schlae/XebecAboveBoard/XebecMem.kicad_sch

## KiCad design XebecMem.kicad_sch (2024-04-21)

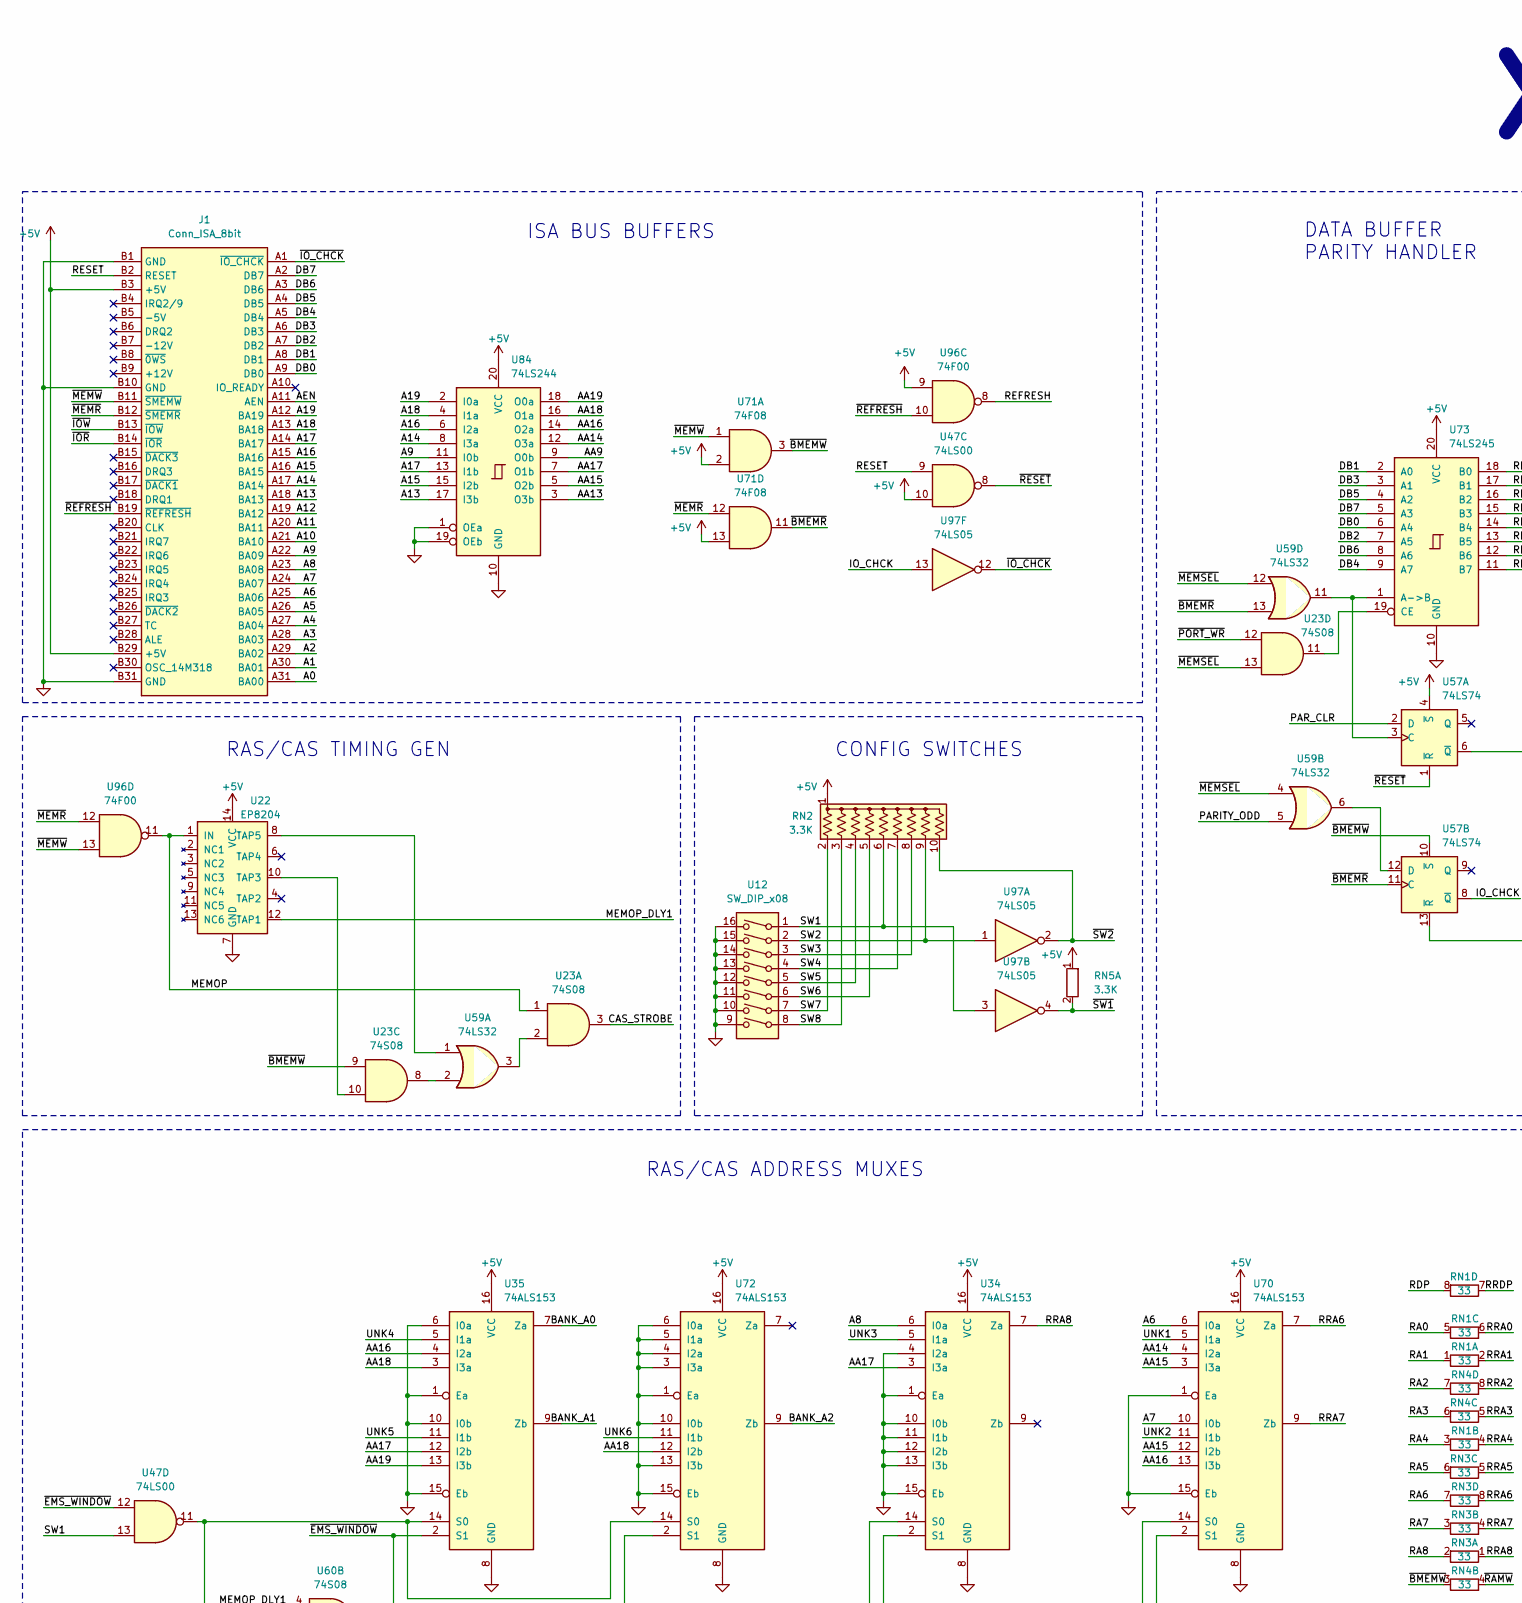
[picture p2: schematic XebecMem.kicad_sch, part in row 1, column 1]

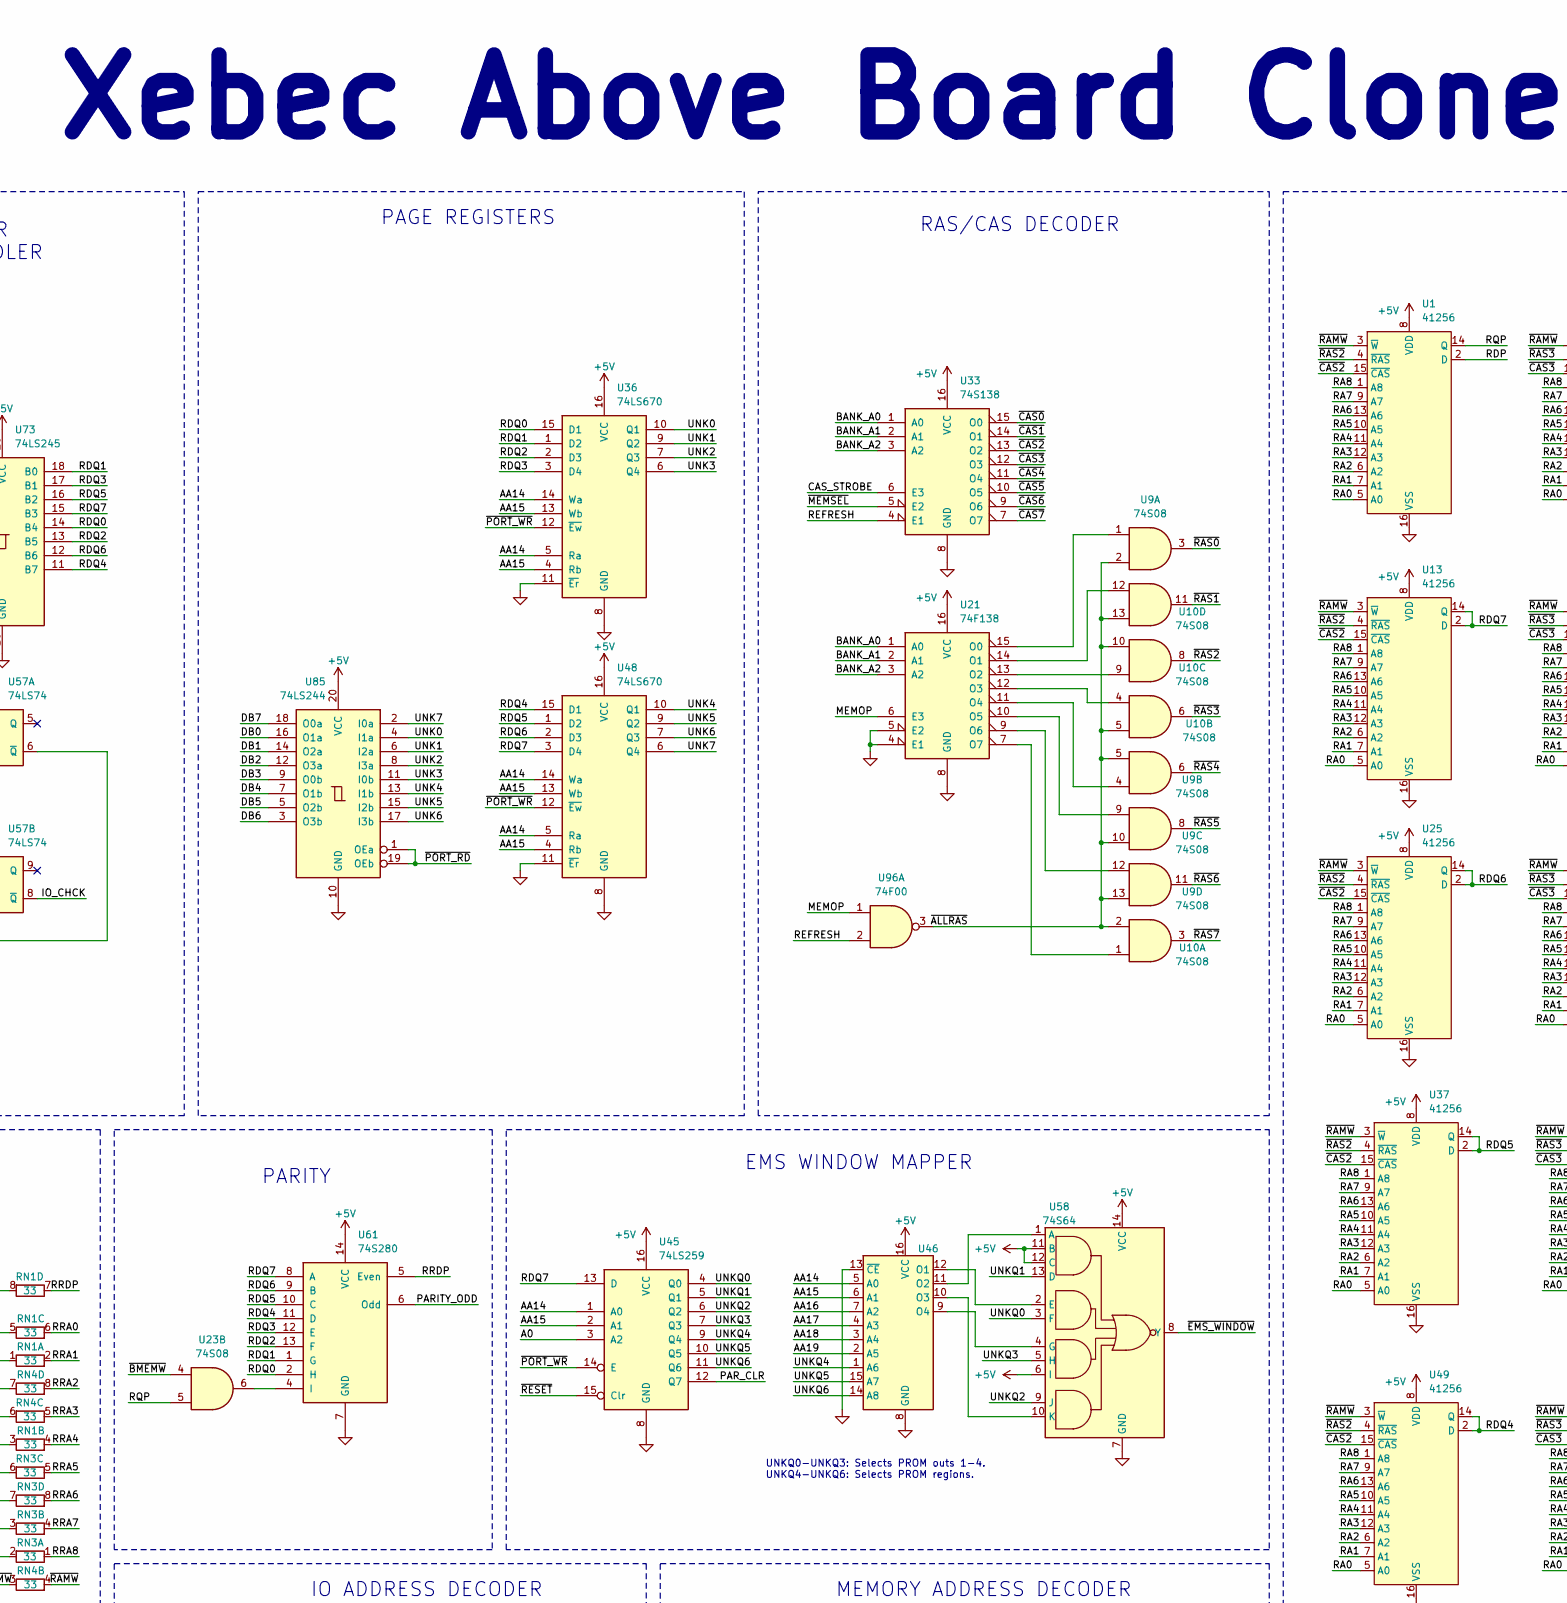
[picture p3: schematic XebecMem.kicad_sch, part in row 1, column 2]

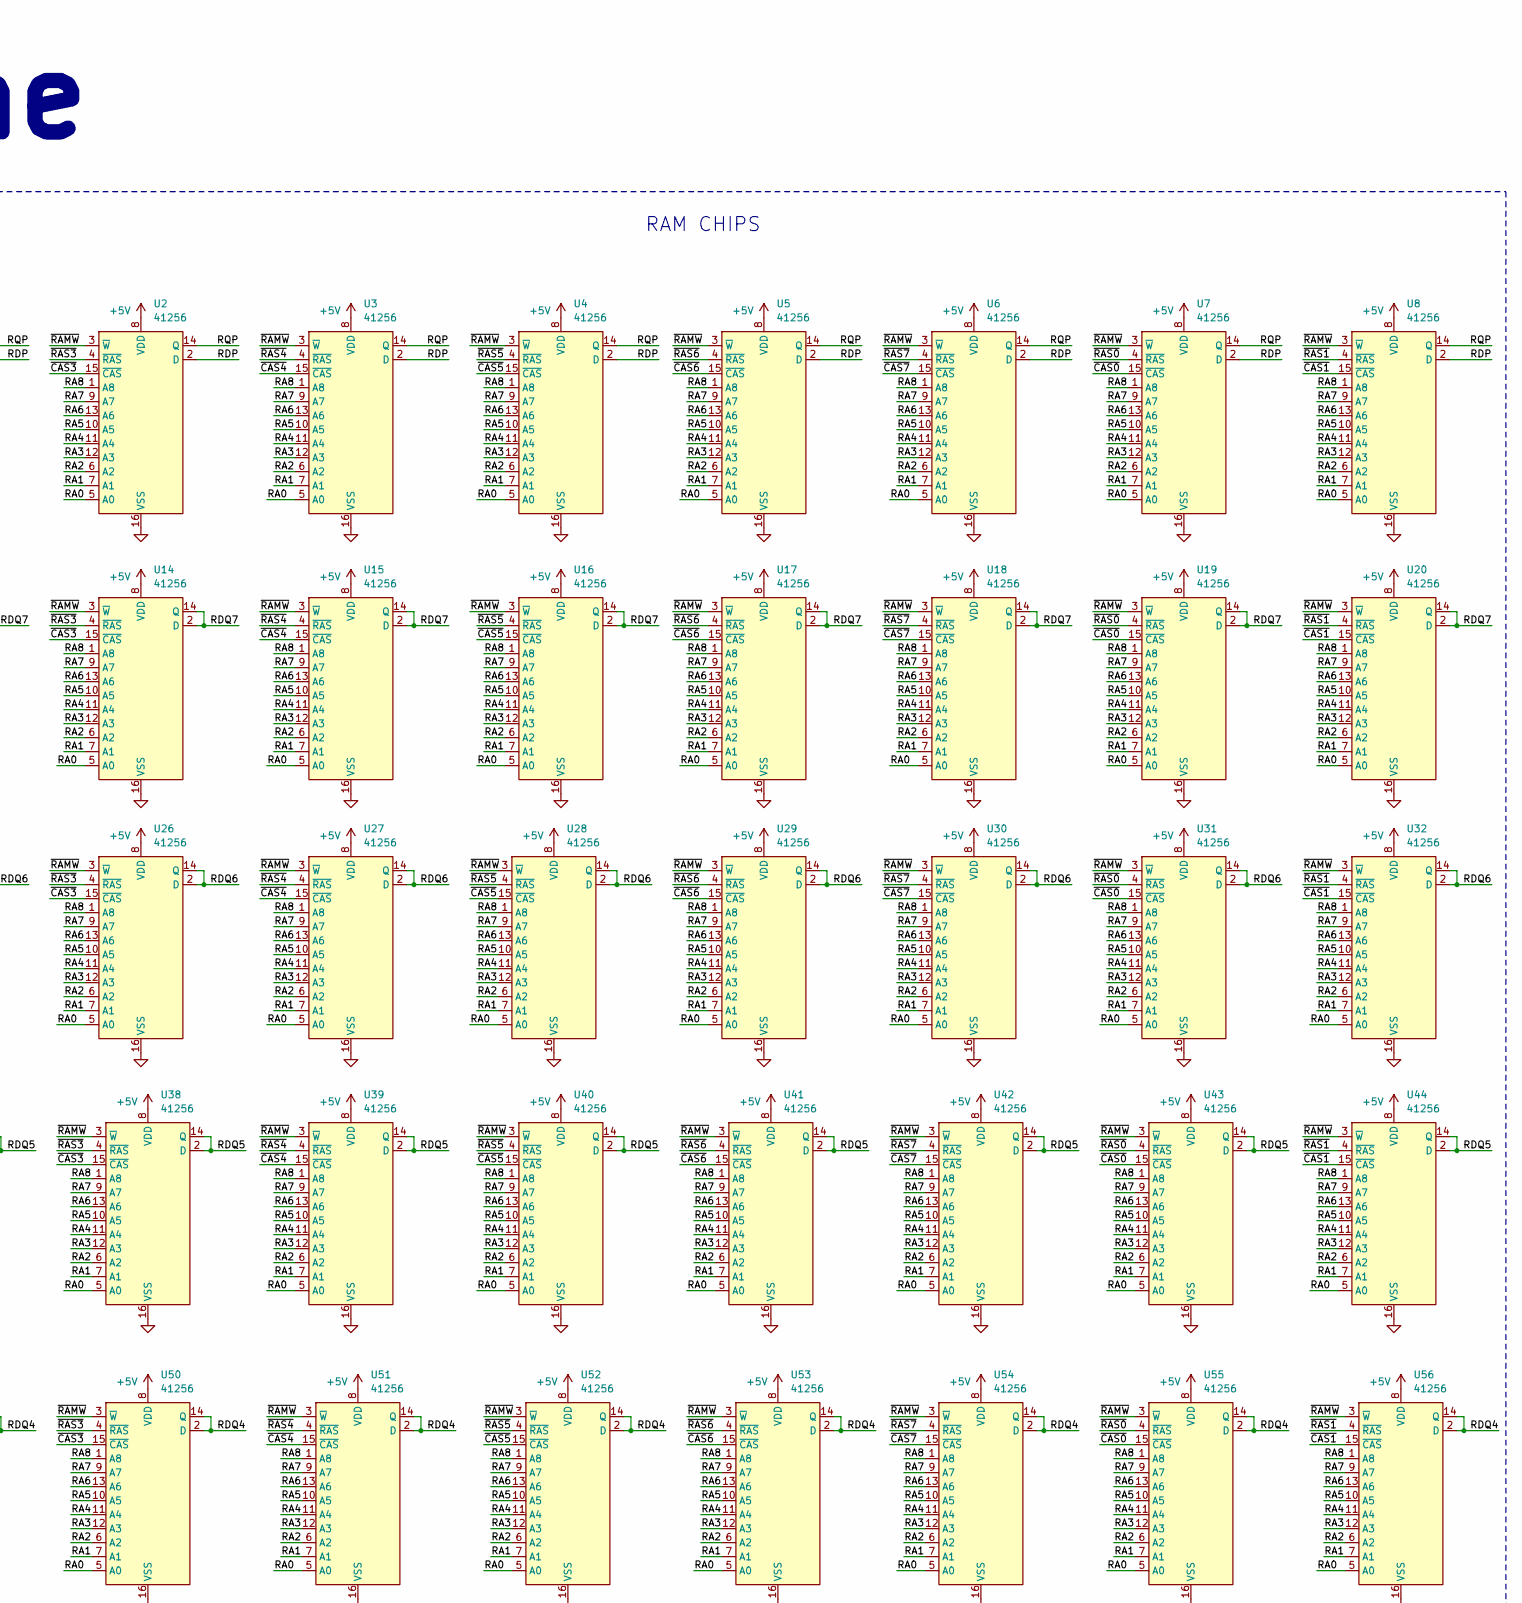
[picture p4: schematic XebecMem.kicad_sch, part in row 1, column 3]

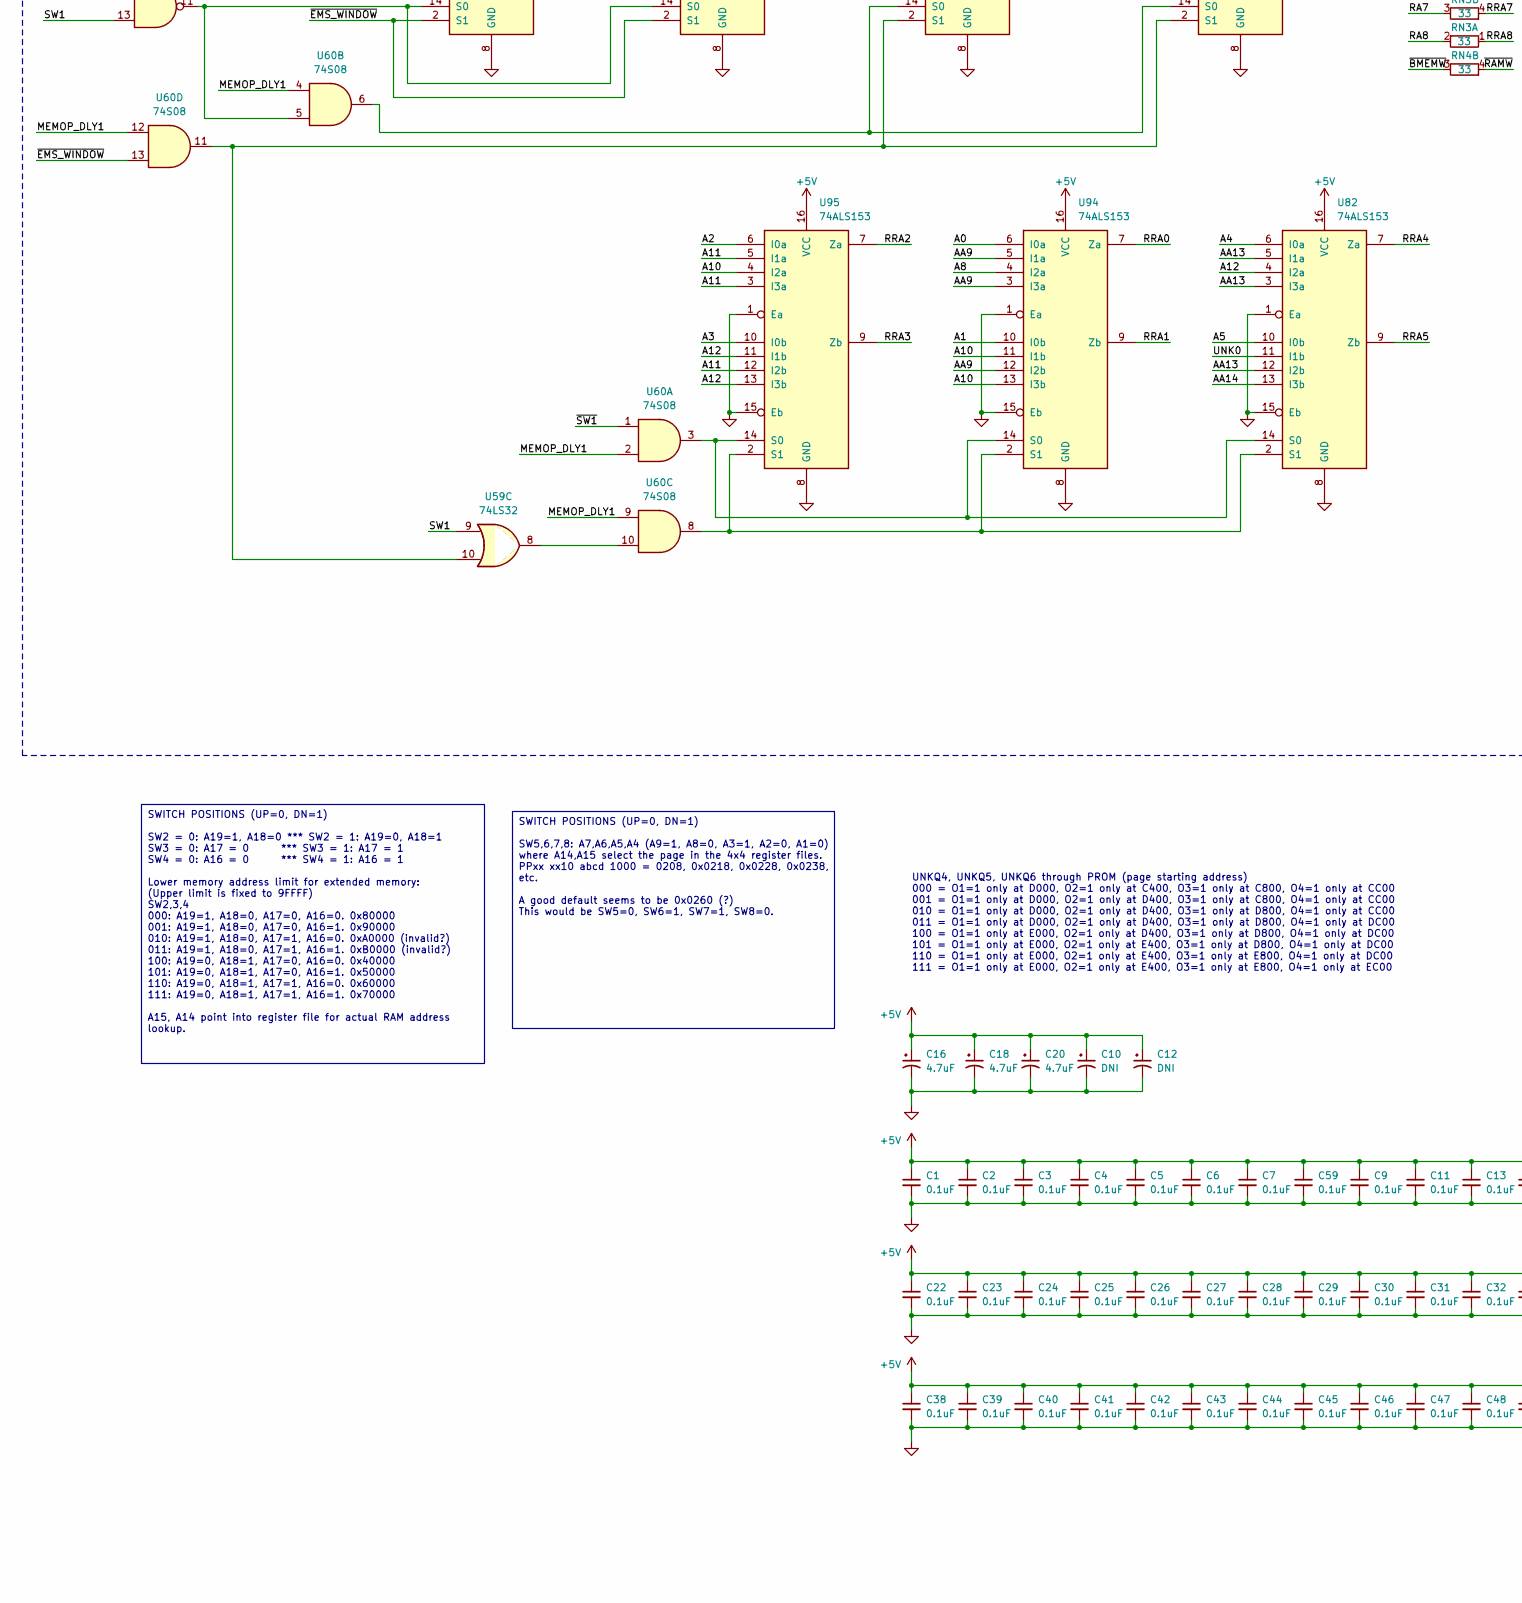
[picture p5: schematic XebecMem.kicad_sch, part in row 2, column 1]

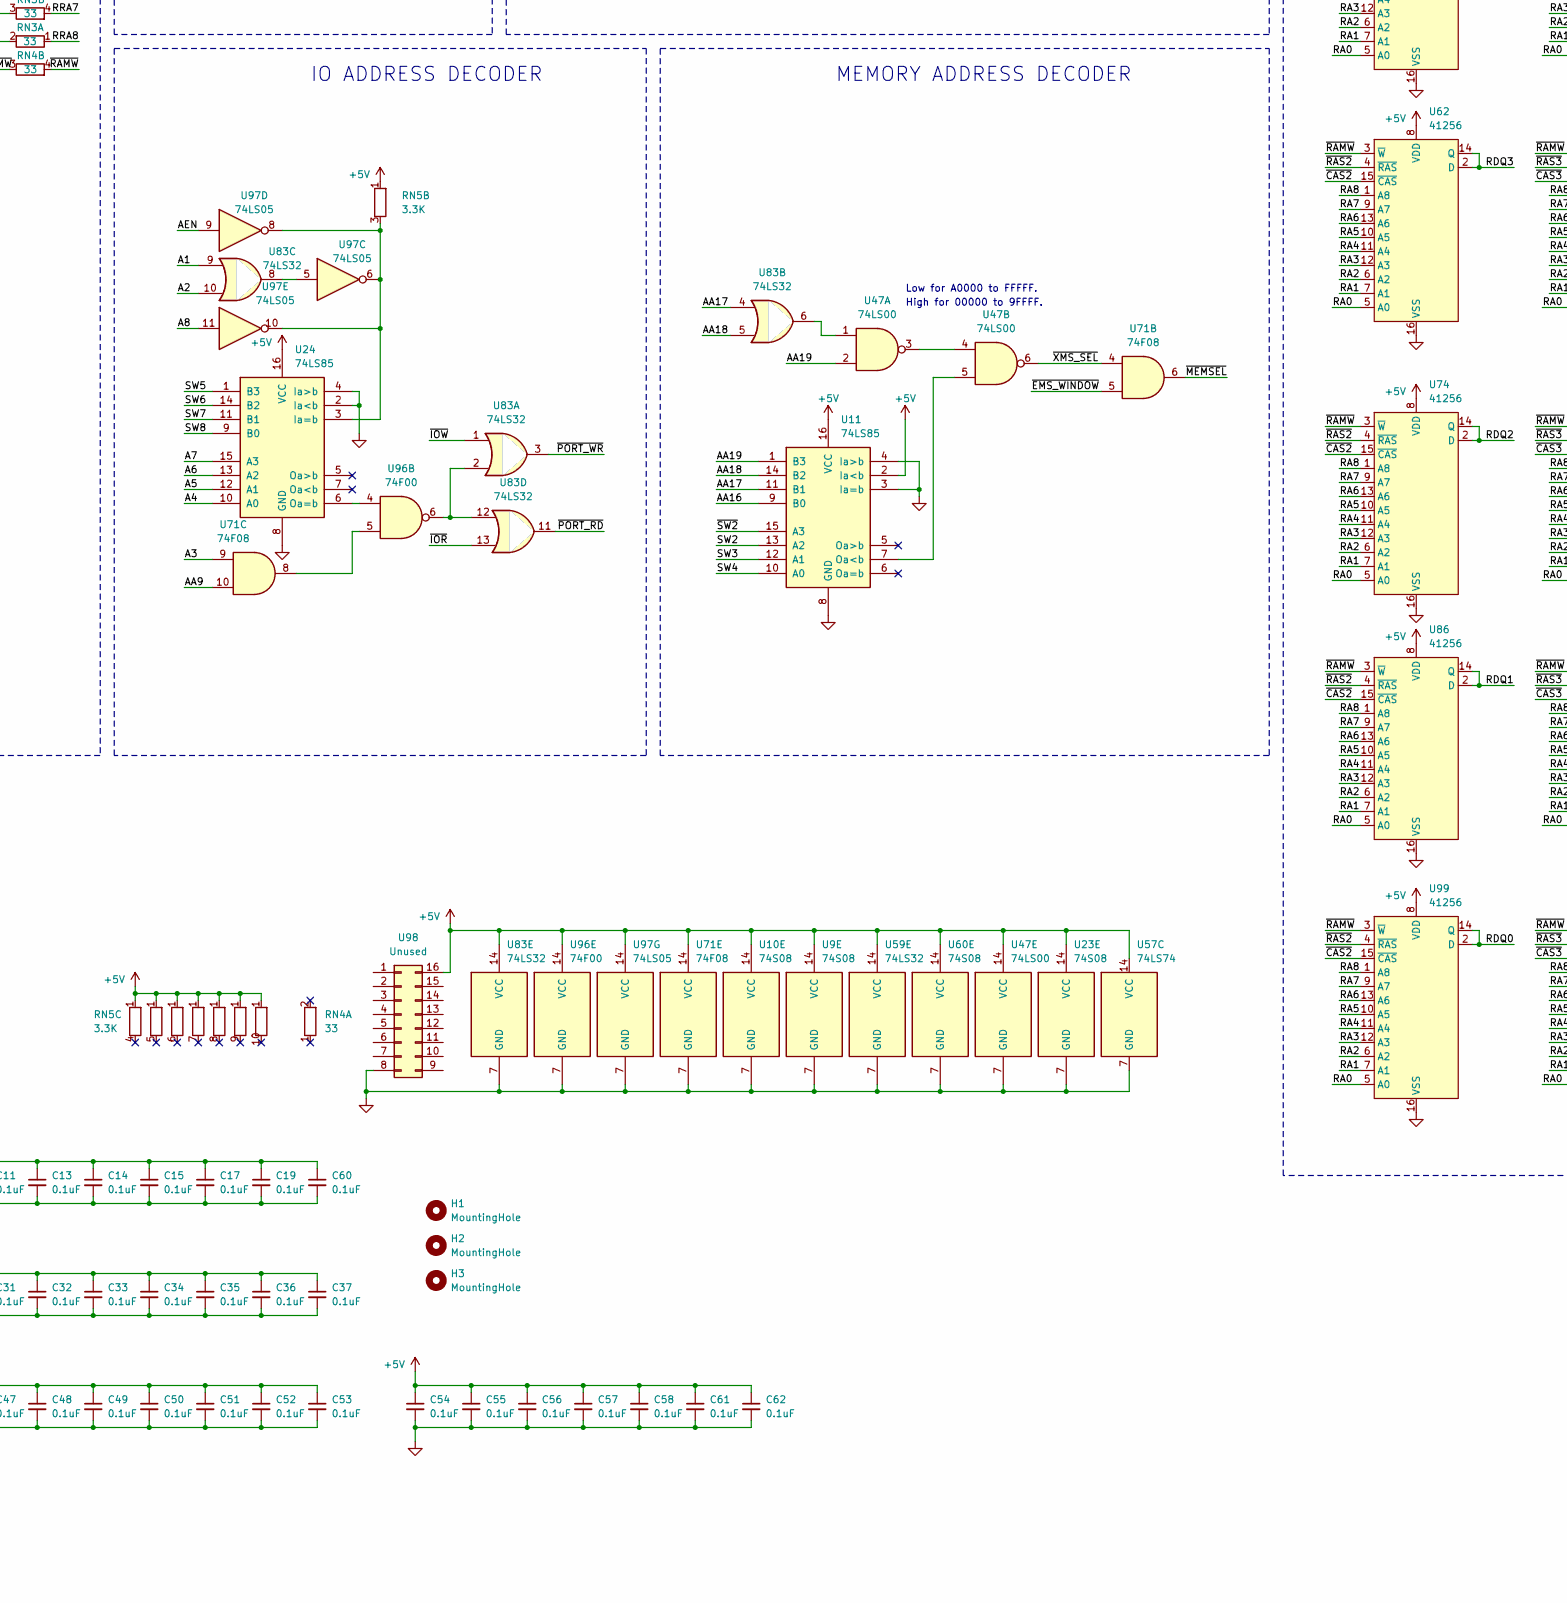
[picture p6: schematic XebecMem.kicad_sch, part in row 2, column 2]

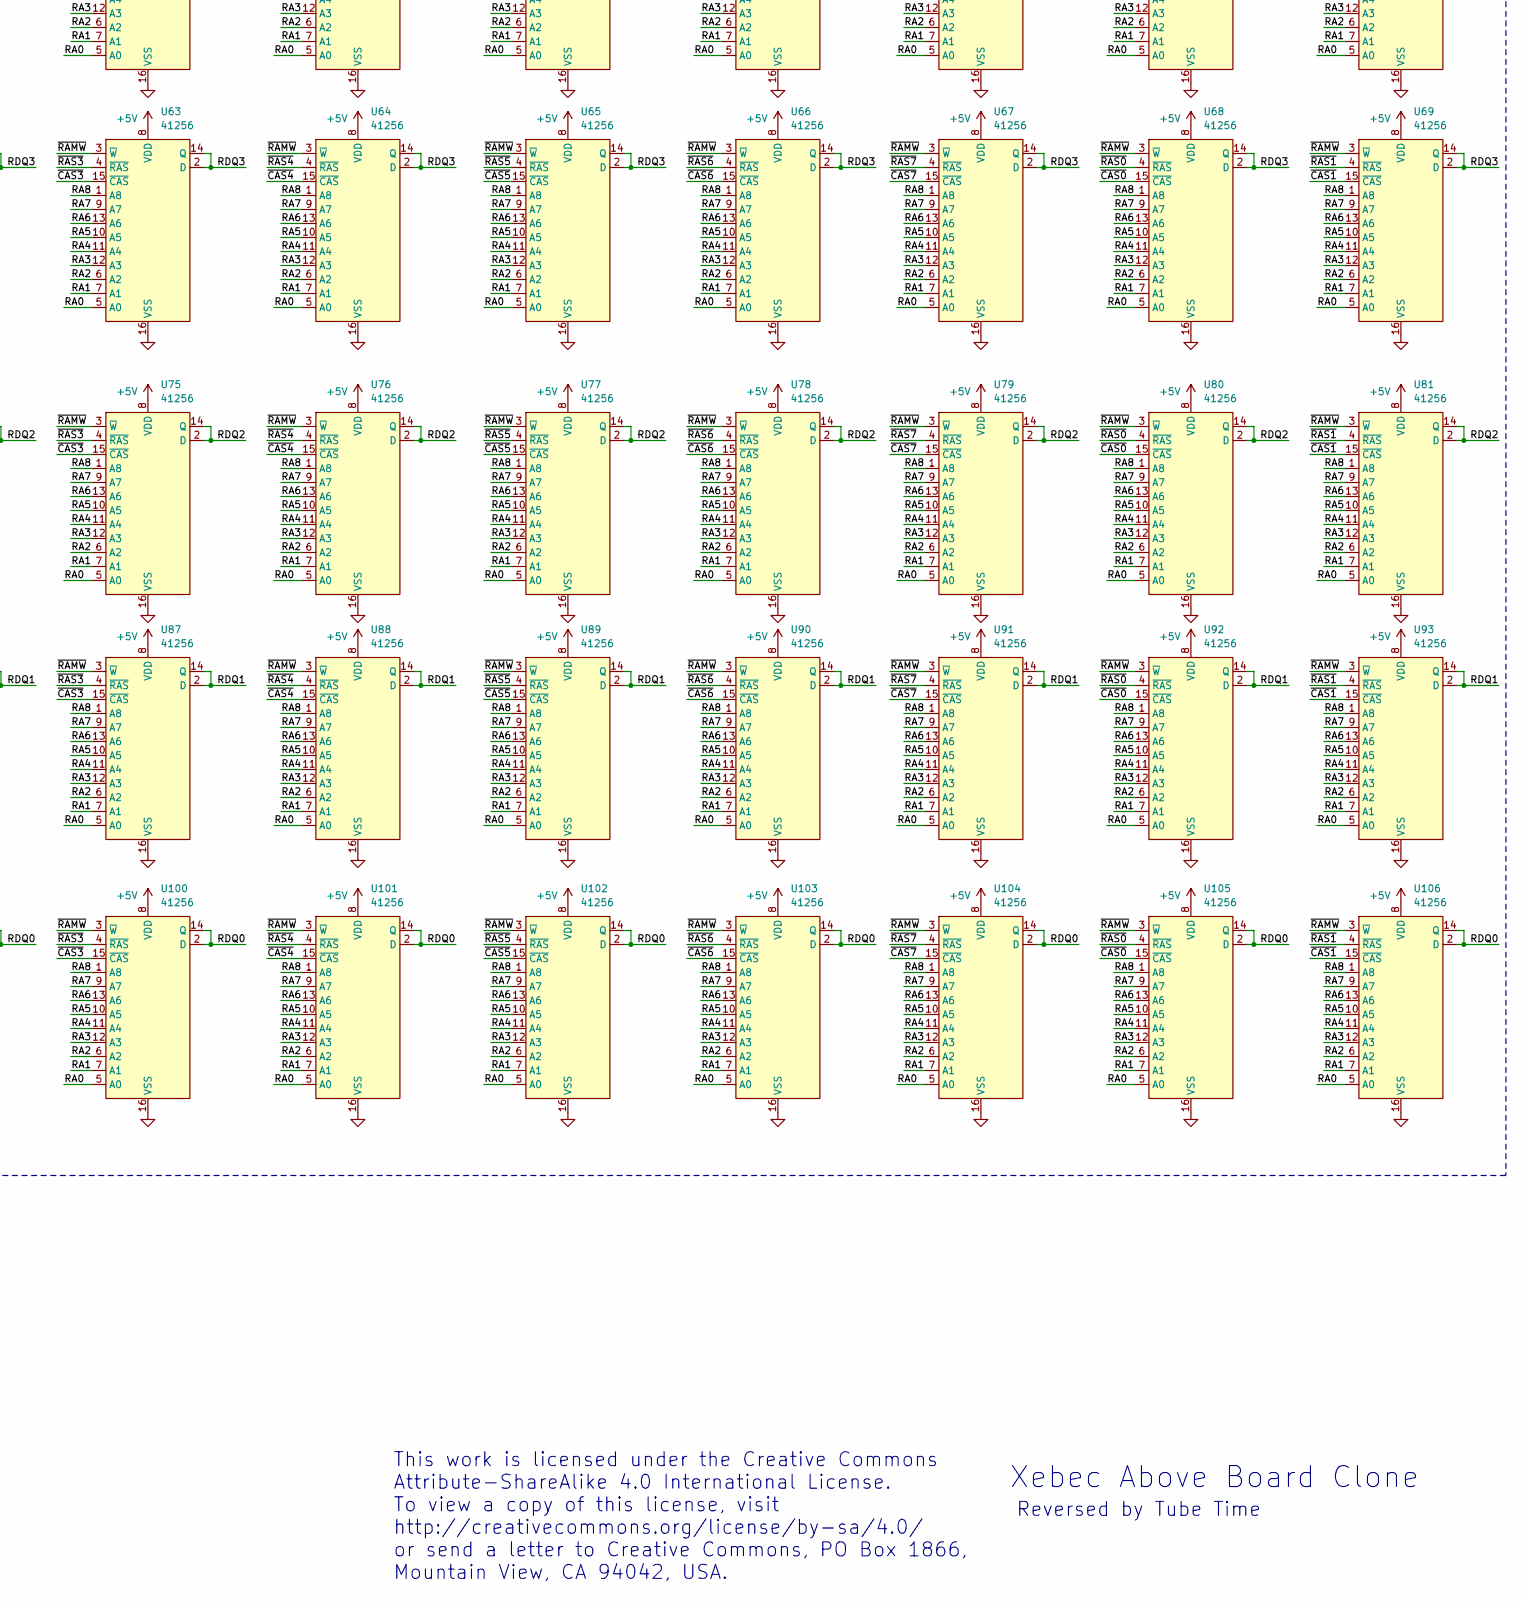
[picture p7: schematic XebecMem.kicad_sch, part in row 2, column 3]

Parts:
C1, C2, C3, C4, C5, C6, C7, C9, C11, C13, C14, C15, C17, C19, C22, C23, C24, C25, C26, C27, C28, C29, C30, C31, C32, C33, C34, C35, C36, C37, C38, C39, C40, C41, C42, C43, C44, C45, C46, C47, C48, C49, C50, C51, C52, C53, C54, C55, C56, C57, C58, C59, C60, C61, C62: 0.1uF; C_Axial_L3.8mm_D2.6mm_P7.50mm_Horizontal
C10, C12: DNI; C_Axial_L3.8mm_D2.6mm_P12.50mm_Horizontal
C16, C18, C20: 4.7uF; C_Axial_L3.8mm_D2.6mm_P12.50mm_Horizontal
H1, H2, H3: MountingHole; MountingHole_3mm
J1: Conn_ISA_8bit; BUS_PC_8BIT
RN1, RN3, RN4: 33; R_Array_SIP8
RN2, RN5: 3.3K; R_Array_SIP10
U1, U2, U3, U4, U5, U6, U7, U8, U13, U14, U15, U16, U17, U18, U19, U20, U25, U26, U27, U28, U29, U30, U31, U32, U37, U38, U39, U40, U41, U42, U43, U44, U49, U50, U51, U52, U53, U54, U55, U56, U62, U63, U64, U65, U66, U67, U68, U69, U74, U75, U76, U77, U78, U79, U80, U81, U86, U87, U88, U89, U90, U91, U92, U93, U99, U100, U101, U102, U103, U104, U105, U106: 41256; DIP254P762X635-16
U9, U10, U23, U60: 74S08; DIP254P762X635-14
U11, U24: 74LS85; DIP254P762X635-16
U12: SW_DIP_x08; DIP254P762X635-16
U21: 74F138; DIP254P762X635-16
U22: EP8204; DIP254P762X635-14
U33: 74S138; DIP254P762X635-16
U34, U35, U70, U72, U82, U94, U95: 74ALS153; DIP254P762X635-16
U36, U48: 74LS670; DIP254P762X635-16
U45: 74LS259; DIP254P762X635-16
U46: DIP254P762X635-16
U47: 74LS00; DIP254P762X635-14
U57: 74LS74; DIP254P762X635-14
U58: 74S64; DIP254P762X635-14
U59, U83: 74LS32; DIP254P762X635-14
U61: 74S280; DIP254P762X635-14
U71: 74F08; DIP254P762X635-14
U73: 74LS245; DIP254P762X635-20
U84, U85: 74LS244; DIP254P762X635-20
U96: 74F00; DIP254P762X635-14
U97: 74LS05; DIP254P762X635-14
U98: Unused; DIP254P762X635-16

Connections:
+5V: C1.1, C2.1, C3.1, C4.1, C5.1, C6.1, C7.1, C9.1, C10.1, C11.1, C12.1, C13.1, C14.1, C15.1, C16.1, C17.1, C18.1, C19.1, C20.1, C22.1, C23.1, C24.1, C25.1, C26.1, C27.1, C28.1, C29.1, C30.1, C31.1, C32.1, C33.1, C34.1, C35.1, C36.1, C37.1, C38.1, C39.1, C40.1, C41.1, C42.1, C43.1, C44.1, C45.1, C46.1, C47.1, C48.1, C49.1, C50.1, C51.1, C52.1, C53.1, C54.1, C55.1, C56.1, C57.1, C58.1, C59.1, C60.1, C61.1, C62.1, J1.B3 (+5V), J1.B29 (+5V), RN2.1 (common), RN5.1 (R1), U1.8 (VDD), U2.8 (VDD), U3.8 (VDD), U4.8 (VDD), U5.8 (VDD), U6.8 (VDD), U7.8 (VDD), U8.8 (VDD), U9.14 (VCC), U10.14 (VCC), U11.2 (Ia<b), U11.16 (VCC), U13.8 (VDD), U14.8 (VDD), U15.8 (VDD), U16.8 (VDD), U17.8 (VDD), U18.8 (VDD), U19.8 (VDD), U20.8 (VDD), U21.16 (VCC), U22.14 (VCC), U23.14 (VCC), U24.16 (VCC), U25.8 (VDD), U26.8 (VDD), U27.8 (VDD), U28.8 (VDD), U29.8 (VDD), U30.8 (VDD), U31.8 (VDD), U32.8 (VDD), U33.16 (VCC), U34.16 (VCC), U35.16 (VCC), U36.16 (VCC), U37.8 (VDD), U38.8 (VDD), U39.8 (VDD), U40.8 (VDD), U41.8 (VDD), U42.8 (VDD), U43.8 (VDD), U44.8 (VDD), U45.16 (VCC), U46.16 (VCC), U47.10, U47.14 (VCC), U48.16 (VCC), U49.8 (VDD), U50.8 (VDD), U51.8 (VDD), U52.8 (VDD), U53.8 (VDD), U54.8 (VDD), U55.8 (VDD), U56.8 (VDD), U57.4 (~S), U57.14 (VCC), U58.6 (I), U58.11 (B), U58.12 (C), U58.14 (VCC), U59.14 (VCC), U60.14 (VCC), U61.14 (VCC), U62.8 (VDD), U63.8 (VDD), U64.8 (VDD), U65.8 (VDD), U66.8 (VDD), U67.8 (VDD), U68.8 (VDD), U69.8 (VDD), U70.16 (VCC), U71.2, U71.13, U71.14 (VCC), U72.16 (VCC), U73.20 (VCC), U74.8 (VDD), U75.8 (VDD), U76.8 (VDD), U77.8 (VDD), U78.8 (VDD), U79.8 (VDD), U80.8 (VDD), U81.8 (VDD), U82.16 (VCC), U83.14 (VCC), U84.20 (VCC), U85.20 (VCC), U86.8 (VDD), U87.8 (VDD), U88.8 (VDD), U89.8 (VDD), U90.8 (VDD), U91.8 (VDD), U92.8 (VDD), U93.8 (VDD), U94.16 (VCC), U95.16 (VCC), U96.9, U96.14 (VCC), U97.14 (VCC), U98.16, U99.8 (VDD), U100.8 (VDD), U101.8 (VDD), U102.8 (VDD), U103.8 (VDD), U104.8 (VDD), U105.8 (VDD), U106.8 (VDD)
A0: J1.A31 (BA00), U45.3 (A2), U94.6 (I0a)
A1: J1.A30 (BA01), U83.9, U94.10 (I0b)
A2: J1.A29 (BA02), U83.10, U95.6 (I0a)
A3: J1.A28 (BA03), U71.9, U95.10 (I0b)
A4: J1.A27 (BA04), U24.10 (A0), U82.6 (I0a)
A5: J1.A26 (BA05), U24.12 (A1), U82.10 (I0b)
A6: J1.A25 (BA06), U24.13 (A2), U70.6 (I0a)
A7: J1.A24 (BA07), U24.15 (A3), U70.10 (I0b)
A8: J1.A23 (BA08), U34.6 (I0a), U94.4 (I2a), U97.11
A9: J1.A22 (BA09), U84.11 (I0b)
A10: J1.A21 (BA10), U94.11 (I1b), U94.13 (I3b), U95.4 (I2a)
A11: J1.A20 (BA11), U95.3 (I3a), U95.5 (I1a), U95.12 (I2b)
A12: J1.A19 (BA12), U82.4 (I2a), U95.11 (I1b), U95.13 (I3b)
A13: J1.A18 (BA13), U84.17 (I3b)
A14: J1.A17 (BA14), U84.8 (I3a)
A15: J1.A16 (BA15), U84.15 (I2b)
A16: J1.A15 (BA16), U84.6 (I2a)
A17: J1.A14 (BA17), U84.13 (I1b)
A18: J1.A13 (BA18), U84.4 (I1a)
A19: J1.A12 (BA19), U84.2 (I0a)
AA9: U71.10, U84.9 (O0b), U94.3 (I3a), U94.5 (I1a), U94.12 (I2b)
AA13: U82.3 (I3a), U82.5 (I1a), U82.12 (I2b), U84.3 (O3b)
AA14: U36.5 (Ra), U36.14 (Wa), U45.1 (A0), U46.5 (A0), U48.5 (Ra), U48.14 (Wa), U70.4 (I2a), U82.13 (I3b), U84.12 (O3a)
AA15: U36.4 (Rb), U36.13 (Wb), U45.2 (A1), U46.6 (A1), U48.4 (Rb), U48.13 (Wb), U70.3 (I3a), U70.12 (I2b), U84.5 (O2b)
AA16: U11.9 (B0), U35.4 (I2a), U46.7 (A2), U70.13 (I3b), U84.14 (O2a)
AA17: U11.11 (B1), U34.3 (I3a), U35.12 (I2b), U46.4 (A3), U83.4, U84.7 (O1b)
AA18: U11.14 (B2), U35.3 (I3a), U46.3 (A4), U72.12 (I2b), U83.5, U84.16 (O1a)
AA19: U11.1 (B3), U35.13 (I3b), U46.2 (A5), U47.2, U84.18 (O0a)
AEN: J1.A11 (AEN), U97.9
BANK_A0: U21.1 (A0), U33.1 (A0), U35.7 (Za)
BANK_A1: U21.2 (A1), U33.2 (A1), U35.9 (Zb)
BANK_A2: U21.3 (A2), U33.3 (A2), U72.9 (Zb)
CAS_STROBE: U23.3, U33.6 (E3)
DB0: J1.A9 (DB0), U73.6 (A4), U85.16 (O1a)
DB1: J1.A8 (DB1), U73.2 (A0), U85.14 (O2a)
DB2: J1.A7 (DB2), U73.7 (A5), U85.12 (O3a)
DB3: J1.A6 (DB3), U73.3 (A1), U85.9 (O0b)
DB4: J1.A5 (DB4), U73.9 (A7), U85.7 (O1b)
DB5: J1.A4 (DB5), U73.4 (A2), U85.5 (O2b)
DB6: J1.A3 (DB6), U73.8 (A6), U85.3 (O3b)
DB7: J1.A2 (DB7), U73.5 (A3), U85.18 (O0a)
GND: C1.2, C2.2, C3.2, C4.2, C5.2, C6.2, C7.2, C9.2, C10.2, C11.2, C12.2, C13.2, C14.2, C15.2, C16.2, C17.2, C18.2, C19.2, C20.2, C22.2, C23.2, C24.2, C25.2, C26.2, C27.2, C28.2, C29.2, C30.2, C31.2, C32.2, C33.2, C34.2, C35.2, C36.2, C37.2, C38.2, C39.2, C40.2, C41.2, C42.2, C43.2, C44.2, C45.2, C46.2, C47.2, C48.2, C49.2, C50.2, C51.2, C52.2, C53.2, C54.2, C55.2, C56.2, C57.2, C58.2, C59.2, C60.2, C61.2, C62.2, J1.B1 (GND), J1.B10 (GND), J1.B31 (GND), U1.16 (VSS), U2.16 (VSS), U3.16 (VSS), U4.16 (VSS), U5.16 (VSS), U6.16 (VSS), U7.16 (VSS), U8.16 (VSS), U9.7 (GND), U10.7 (GND), U11.3 (Ia=b), U11.4 (Ia>b), U11.8 (GND), U12.9, U12.10, U12.11, U12.12, U12.13, U12.14, U12.15, U12.16, U13.16 (VSS), U14.16 (VSS), U15.16 (VSS), U16.16 (VSS), U17.16 (VSS), U18.16 (VSS), U19.16 (VSS), U20.16 (VSS), U21.4 (E1), U21.5 (E2), U21.8 (GND), U22.7 (GND), U23.7 (GND), U24.2 (Ia<b), U24.4 (Ia>b), U24.8 (GND), U25.16 (VSS), U26.16 (VSS), U27.16 (VSS), U28.16 (VSS), U29.16 (VSS), U30.16 (VSS), U31.16 (VSS), U32.16 (VSS), U33.8 (GND), U34.1 (Ea), U34.4 (I2a), U34.8 (GND), U34.10 (I0b), U34.11 (I1b), U34.12 (I2b), U34.13 (I3b), U34.15 (Eb), U35.1 (Ea), U35.6 (I0a), U35.8 (GND), U35.10 (I0b), U35.15 (Eb), U36.8 (GND), U36.11 (~Er), U37.16 (VSS), U38.16 (VSS), U39.16 (VSS), U40.16 (VSS), U41.16 (VSS), U42.16 (VSS), U43.16 (VSS), U44.16 (VSS), U45.8 (GND), U46.8 (GND), U46.13 (~CE), U47.7 (GND), U48.8 (GND), U48.11 (~Er), U49.16 (VSS), U50.16 (VSS), U51.16 (VSS), U52.16 (VSS), U53.16 (VSS), U54.16 (VSS), U55.16 (VSS), U56.16 (VSS), U57.7 (GND), U58.7 (GND), U59.7 (GND), U60.7 (GND), U61.7 (GND), U62.16 (VSS), U63.16 (VSS), U64.16 (VSS), U65.16 (VSS), U66.16 (VSS), U67.16 (VSS), U68.16 (VSS), U69.16 (VSS), U70.1 (Ea), U70.8 (GND), U70.15 (Eb), U71.7 (GND), U72.1 (Ea), U72.3 (I3a), U72.4 (I2a), U72.5 (I1a), U72.6 (I0a), U72.8 (GND), U72.10 (I0b), U72.13 (I3b), U72.15 (Eb), U73.10 (GND), U74.16 (VSS), U75.16 (VSS), U76.16 (VSS), U77.16 (VSS), U78.16 (VSS), U79.16 (VSS), U80.16 (VSS), U81.16 (VSS), U82.1 (Ea), U82.8 (GND), U82.15 (Eb), U83.7 (GND), U84.1 (OEa), U84.10 (GND), U84.19 (OEb), U85.10 (GND), U86.16 (VSS), U87.16 (VSS), U88.16 (VSS), U89.16 (VSS), U90.16 (VSS), U91.16 (VSS), U92.16 (VSS), U93.16 (VSS), U94.1 (Ea), U94.8 (GND), U94.15 (Eb), U95.1 (Ea), U95.8 (GND), U95.15 (Eb), U96.7 (GND), U97.7 (GND), U98.8, U99.16 (VSS), U100.16 (VSS), U101.16 (VSS), U102.16 (VSS), U103.16 (VSS), U104.16 (VSS), U105.16 (VSS), U106.16 (VSS)
IO_CHCK: U57.8 (~Q), U97.13
MEMOP: U21.6 (E3), U22.1 (IN), U23.1, U96.1, U96.11
MEMOP_DLY1: U22.12 (TAP1), U60.2, U60.4, U60.9, U60.12
unnamed: RN5.3 (R2.2), U24.3 (Ia=b), U97.6, U97.8, U97.10
unnamed: U10.1, U21.7 (O7)
unnamed: U10.4, U21.12 (O3)
unnamed: U10.9, U21.13 (O2)
unnamed: U10.12, U21.14 (O1)
unnamed: U11.7 (Oa<b), U47.5
unnamed: U9.12, U21.9 (O6)
unnamed: U9.9, U21.10 (O5)
unnamed: U9.4, U21.11 (O4)
unnamed: U9.1, U21.15 (O0)
unnamed: U22.8 (TAP5), U59.1
unnamed: U22.10 (TAP3), U23.10
unnamed: U23.2, U59.3
unnamed: U23.6, U61.4 (I)
unnamed: U23.8, U59.2
unnamed: U23.11, U73.19 (CE)
unnamed: U24.6 (Oa=b), U96.4
unnamed: U34.2 (S1), U59.10, U60.11, U70.2 (S1)
unnamed: U34.14 (S0), U60.6, U70.14 (S0)
unnamed: U35.14 (S0), U47.11, U60.5, U72.14 (S0)
unnamed: U46.9 (O4), U58.4 (G)
unnamed: U46.10 (O3), U58.10 (K)
unnamed: U46.11 (O2), U58.1 (A)
unnamed: U46.12 (O1), U58.2 (E)
unnamed: U47.1, U83.6
unnamed: U47.3, U47.4
unnamed: U57.3 (C), U59.11, U73.1 (A->B)
unnamed: U57.12 (D), U59.6
unnamed: U57.6 (~Q), U57.13 (~R)
unnamed: U59.8, U60.10
unnamed: U60.3, U82.14 (S0), U94.14 (S0), U95.14 (S0)
unnamed: U60.8, U82.2 (S1), U94.2 (S1), U95.2 (S1)
unnamed: U71.8, U96.5
unnamed: U83.8, U97.5
unnamed: U83.2, U83.12, U96.6
PARITY_ODD: U59.5, U61.6 (Odd)
PAR_CLR: U45.12 (Q7), U57.2 (D)
RA0: RN1.5 (R3.1), U1.5 (A0), U2.5 (A0), U3.5 (A0), U4.5 (A0), U5.5 (A0), U6.5 (A0), U7.5 (A0), U8.5 (A0), U13.5 (A0), U14.5 (A0), U15.5 (A0), U16.5 (A0), U17.5 (A0), U18.5 (A0), U19.5 (A0), U20.5 (A0), U25.5 (A0), U26.5 (A0), U27.5 (A0), U28.5 (A0), U29.5 (A0), U30.5 (A0), U31.5 (A0), U32.5 (A0), U37.5 (A0), U38.5 (A0), U39.5 (A0), U40.5 (A0), U41.5 (A0), U42.5 (A0), U43.5 (A0), U44.5 (A0), U49.5 (A0), U50.5 (A0), U51.5 (A0), U52.5 (A0), U53.5 (A0), U54.5 (A0), U55.5 (A0), U56.5 (A0), U62.5 (A0), U63.5 (A0), U64.5 (A0), U65.5 (A0), U66.5 (A0), U67.5 (A0), U68.5 (A0), U69.5 (A0), U74.5 (A0), U75.5 (A0), U76.5 (A0), U77.5 (A0), U78.5 (A0), U79.5 (A0), U80.5 (A0), U81.5 (A0), U86.5 (A0), U87.5 (A0), U88.5 (A0), U89.5 (A0), U90.5 (A0), U91.5 (A0), U92.5 (A0), U93.5 (A0), U99.5 (A0), U100.5 (A0), U101.5 (A0), U102.5 (A0), U103.5 (A0), U104.5 (A0), U105.5 (A0), U106.5 (A0)
RA1: RN1.1 (R1.1), U1.7 (A1), U2.7 (A1), U3.7 (A1), U4.7 (A1), U5.7 (A1), U6.7 (A1), U7.7 (A1), U8.7 (A1), U13.7 (A1), U14.7 (A1), U15.7 (A1), U16.7 (A1), U17.7 (A1), U18.7 (A1), U19.7 (A1), U20.7 (A1), U25.7 (A1), U26.7 (A1), U27.7 (A1), U28.7 (A1), U29.7 (A1), U30.7 (A1), U31.7 (A1), U32.7 (A1), U37.7 (A1), U38.7 (A1), U39.7 (A1), U40.7 (A1), U41.7 (A1), U42.7 (A1), U43.7 (A1), U44.7 (A1), U49.7 (A1), U50.7 (A1), U51.7 (A1), U52.7 (A1), U53.7 (A1), U54.7 (A1), U55.7 (A1), U56.7 (A1), U62.7 (A1), U63.7 (A1), U64.7 (A1), U65.7 (A1), U66.7 (A1), U67.7 (A1), U68.7 (A1), U69.7 (A1), U74.7 (A1), U75.7 (A1), U76.7 (A1), U77.7 (A1), U78.7 (A1), U79.7 (A1), U80.7 (A1), U81.7 (A1), U86.7 (A1), U87.7 (A1), U88.7 (A1), U89.7 (A1), U90.7 (A1), U91.7 (A1), U92.7 (A1), U93.7 (A1), U99.7 (A1), U100.7 (A1), U101.7 (A1), U102.7 (A1), U103.7 (A1), U104.7 (A1), U105.7 (A1), U106.7 (A1)
RA2: RN4.7 (R4.1), U1.6 (A2), U2.6 (A2), U3.6 (A2), U4.6 (A2), U5.6 (A2), U6.6 (A2), U7.6 (A2), U8.6 (A2), U13.6 (A2), U14.6 (A2), U15.6 (A2), U16.6 (A2), U17.6 (A2), U18.6 (A2), U19.6 (A2), U20.6 (A2), U25.6 (A2), U26.6 (A2), U27.6 (A2), U28.6 (A2), U29.6 (A2), U30.6 (A2), U31.6 (A2), U32.6 (A2), U37.6 (A2), U38.6 (A2), U39.6 (A2), U40.6 (A2), U41.6 (A2), U42.6 (A2), U43.6 (A2), U44.6 (A2), U49.6 (A2), U50.6 (A2), U51.6 (A2), U52.6 (A2), U53.6 (A2), U54.6 (A2), U55.6 (A2), U56.6 (A2), U62.6 (A2), U63.6 (A2), U64.6 (A2), U65.6 (A2), U66.6 (A2), U67.6 (A2), U68.6 (A2), U69.6 (A2), U74.6 (A2), U75.6 (A2), U76.6 (A2), U77.6 (A2), U78.6 (A2), U79.6 (A2), U80.6 (A2), U81.6 (A2), U86.6 (A2), U87.6 (A2), U88.6 (A2), U89.6 (A2), U90.6 (A2), U91.6 (A2), U92.6 (A2), U93.6 (A2), U99.6 (A2), U100.6 (A2), U101.6 (A2), U102.6 (A2), U103.6 (A2), U104.6 (A2), U105.6 (A2), U106.6 (A2)
RA3: RN4.6 (R3.2), U1.12 (A3), U2.12 (A3), U3.12 (A3), U4.12 (A3), U5.12 (A3), U6.12 (A3), U7.12 (A3), U8.12 (A3), U13.12 (A3), U14.12 (A3), U15.12 (A3), U16.12 (A3), U17.12 (A3), U18.12 (A3), U19.12 (A3), U20.12 (A3), U25.12 (A3), U26.12 (A3), U27.12 (A3), U28.12 (A3), U29.12 (A3), U30.12 (A3), U31.12 (A3), U32.12 (A3), U37.12 (A3), U38.12 (A3), U39.12 (A3), U40.12 (A3), U41.12 (A3), U42.12 (A3), U43.12 (A3), U44.12 (A3), U49.12 (A3), U50.12 (A3), U51.12 (A3), U52.12 (A3), U53.12 (A3), U54.12 (A3), U55.12 (A3), U56.12 (A3), U62.12 (A3), U63.12 (A3), U64.12 (A3), U65.12 (A3), U66.12 (A3), U67.12 (A3), U68.12 (A3), U69.12 (A3), U74.12 (A3), U75.12 (A3), U76.12 (A3), U77.12 (A3), U78.12 (A3), U79.12 (A3), U80.12 (A3), U81.12 (A3), U86.12 (A3), U87.12 (A3), U88.12 (A3), U89.12 (A3), U90.12 (A3), U91.12 (A3), U92.12 (A3), U93.12 (A3), U99.12 (A3), U100.12 (A3), U101.12 (A3), U102.12 (A3), U103.12 (A3), U104.12 (A3), U105.12 (A3), U106.12 (A3)
RA4: RN1.3 (R2.1), U1.11 (A4), U2.11 (A4), U3.11 (A4), U4.11 (A4), U5.11 (A4), U6.11 (A4), U7.11 (A4), U8.11 (A4), U13.11 (A4), U14.11 (A4), U15.11 (A4), U16.11 (A4), U17.11 (A4), U18.11 (A4), U19.11 (A4), U20.11 (A4), U25.11 (A4), U26.11 (A4), U27.11 (A4), U28.11 (A4), U29.11 (A4), U30.11 (A4), U31.11 (A4), U32.11 (A4), U37.11 (A4), U38.11 (A4), U39.11 (A4), U40.11 (A4), U41.11 (A4), U42.11 (A4), U43.11 (A4), U44.11 (A4), U49.11 (A4), U50.11 (A4), U51.11 (A4), U52.11 (A4), U53.11 (A4), U54.11 (A4), U55.11 (A4), U56.11 (A4), U62.11 (A4), U63.11 (A4), U64.11 (A4), U65.11 (A4), U66.11 (A4), U67.11 (A4), U68.11 (A4), U69.11 (A4), U74.11 (A4), U75.11 (A4), U76.11 (A4), U77.11 (A4), U78.11 (A4), U79.11 (A4), U80.11 (A4), U81.11 (A4), U86.11 (A4), U87.11 (A4), U88.11 (A4), U89.11 (A4), U90.11 (A4), U91.11 (A4), U92.11 (A4), U93.11 (A4), U99.11 (A4), U100.11 (A4), U101.11 (A4), U102.11 (A4), U103.11 (A4), U104.11 (A4), U105.11 (A4), U106.11 (A4)
RA5: RN3.6 (R3.2), U1.10 (A5), U2.10 (A5), U3.10 (A5), U4.10 (A5), U5.10 (A5), U6.10 (A5), U7.10 (A5), U8.10 (A5), U13.10 (A5), U14.10 (A5), U15.10 (A5), U16.10 (A5), U17.10 (A5), U18.10 (A5), U19.10 (A5), U20.10 (A5), U25.10 (A5), U26.10 (A5), U27.10 (A5), U28.10 (A5), U29.10 (A5), U30.10 (A5), U31.10 (A5), U32.10 (A5), U37.10 (A5), U38.10 (A5), U39.10 (A5), U40.10 (A5), U41.10 (A5), U42.10 (A5), U43.10 (A5), U44.10 (A5), U49.10 (A5), U50.10 (A5), U51.10 (A5), U52.10 (A5), U53.10 (A5), U54.10 (A5), U55.10 (A5), U56.10 (A5), U62.10 (A5), U63.10 (A5), U64.10 (A5), U65.10 (A5), U66.10 (A5), U67.10 (A5), U68.10 (A5), U69.10 (A5), U74.10 (A5), U75.10 (A5), U76.10 (A5), U77.10 (A5), U78.10 (A5), U79.10 (A5), U80.10 (A5), U81.10 (A5), U86.10 (A5), U87.10 (A5), U88.10 (A5), U89.10 (A5), U90.10 (A5), U91.10 (A5), U92.10 (A5), U93.10 (A5), U99.10 (A5), U100.10 (A5), U101.10 (A5), U102.10 (A5), U103.10 (A5), U104.10 (A5), U105.10 (A5), U106.10 (A5)
RA6: RN3.7 (R4.1), U1.13 (A6), U2.13 (A6), U3.13 (A6), U4.13 (A6), U5.13 (A6), U6.13 (A6), U7.13 (A6), U8.13 (A6), U13.13 (A6), U14.13 (A6), U15.13 (A6), U16.13 (A6), U17.13 (A6), U18.13 (A6), U19.13 (A6), U20.13 (A6), U25.13 (A6), U26.13 (A6), U27.13 (A6), U28.13 (A6), U29.13 (A6), U30.13 (A6), U31.13 (A6), U32.13 (A6), U37.13 (A6), U38.13 (A6), U39.13 (A6), U40.13 (A6), U41.13 (A6), U42.13 (A6), U43.13 (A6), U44.13 (A6), U49.13 (A6), U50.13 (A6), U51.13 (A6), U52.13 (A6), U53.13 (A6), U54.13 (A6), U55.13 (A6), U56.13 (A6), U62.13 (A6), U63.13 (A6), U64.13 (A6), U65.13 (A6), U66.13 (A6), U67.13 (A6), U68.13 (A6), U69.13 (A6), U74.13 (A6), U75.13 (A6), U76.13 (A6), U77.13 (A6), U78.13 (A6), U79.13 (A6), U80.13 (A6), U81.13 (A6), U86.13 (A6), U87.13 (A6), U88.13 (A6), U89.13 (A6), U90.13 (A6), U91.13 (A6), U92.13 (A6), U93.13 (A6), U99.13 (A6), U100.13 (A6), U101.13 (A6), U102.13 (A6), U103.13 (A6), U104.13 (A6), U105.13 (A6), U106.13 (A6)
RA7: RN3.3 (R2.1), U1.9 (A7), U2.9 (A7), U3.9 (A7), U4.9 (A7), U5.9 (A7), U6.9 (A7), U7.9 (A7), U8.9 (A7), U13.9 (A7), U14.9 (A7), U15.9 (A7), U16.9 (A7), U17.9 (A7), U18.9 (A7), U19.9 (A7), U20.9 (A7), U25.9 (A7), U26.9 (A7), U27.9 (A7), U28.9 (A7), U29.9 (A7), U30.9 (A7), U31.9 (A7), U32.9 (A7), U37.9 (A7), U38.9 (A7), U39.9 (A7), U40.9 (A7), U41.9 (A7), U42.9 (A7), U43.9 (A7), U44.9 (A7), U49.9 (A7), U50.9 (A7), U51.9 (A7), U52.9 (A7), U53.9 (A7), U54.9 (A7), U55.9 (A7), U56.9 (A7), U62.9 (A7), U63.9 (A7), U64.9 (A7), U65.9 (A7), U66.9 (A7), U67.9 (A7), U68.9 (A7), U69.9 (A7), U74.9 (A7), U75.9 (A7), U76.9 (A7), U77.9 (A7), U78.9 (A7), U79.9 (A7), U80.9 (A7), U81.9 (A7), U86.9 (A7), U87.9 (A7), U88.9 (A7), U89.9 (A7), U90.9 (A7), U91.9 (A7), U92.9 (A7), U93.9 (A7), U99.9 (A7), U100.9 (A7), U101.9 (A7), U102.9 (A7), U103.9 (A7), U104.9 (A7), U105.9 (A7), U106.9 (A7)
RA8: RN3.2 (R1.2), U1.1 (A8), U2.1 (A8), U3.1 (A8), U4.1 (A8), U5.1 (A8), U6.1 (A8), U7.1 (A8), U8.1 (A8), U13.1 (A8), U14.1 (A8), U15.1 (A8), U16.1 (A8), U17.1 (A8), U18.1 (A8), U19.1 (A8), U20.1 (A8), U25.1 (A8), U26.1 (A8), U27.1 (A8), U28.1 (A8), U29.1 (A8), U30.1 (A8), U31.1 (A8), U32.1 (A8), U37.1 (A8), U38.1 (A8), U39.1 (A8), U40.1 (A8), U41.1 (A8), U42.1 (A8), U43.1 (A8), U44.1 (A8), U49.1 (A8), U50.1 (A8), U51.1 (A8), U52.1 (A8), U53.1 (A8), U54.1 (A8), U55.1 (A8), U56.1 (A8), U62.1 (A8), U63.1 (A8), U64.1 (A8), U65.1 (A8), U66.1 (A8), U67.1 (A8), U68.1 (A8), U69.1 (A8), U74.1 (A8), U75.1 (A8), U76.1 (A8), U77.1 (A8), U78.1 (A8), U79.1 (A8), U80.1 (A8), U81.1 (A8), U86.1 (A8), U87.1 (A8), U88.1 (A8), U89.1 (A8), U90.1 (A8), U91.1 (A8), U92.1 (A8), U93.1 (A8), U99.1 (A8), U100.1 (A8), U101.1 (A8), U102.1 (A8), U103.1 (A8), U104.1 (A8), U105.1 (A8), U106.1 (A8)
RDP: RN1.8 (R4.2), U1.2 (D), U2.2 (D), U3.2 (D), U4.2 (D), U5.2 (D), U6.2 (D), U7.2 (D), U8.2 (D)
RDQ0: U36.15 (D1), U61.2 (H), U73.14 (B4), U99.2 (D), U99.14 (Q), U100.2 (D), U100.14 (Q), U101.2 (D), U101.14 (Q), U102.2 (D), U102.14 (Q), U103.2 (D), U103.14 (Q), U104.2 (D), U104.14 (Q), U105.2 (D), U105.14 (Q), U106.2 (D), U106.14 (Q)
RDQ1: U36.1 (D2), U61.1 (G), U73.18 (B0), U86.2 (D), U86.14 (Q), U87.2 (D), U87.14 (Q), U88.2 (D), U88.14 (Q), U89.2 (D), U89.14 (Q), U90.2 (D), U90.14 (Q), U91.2 (D), U91.14 (Q), U92.2 (D), U92.14 (Q), U93.2 (D), U93.14 (Q)
RDQ2: U36.2 (D3), U61.13 (F), U73.13 (B5), U74.2 (D), U74.14 (Q), U75.2 (D), U75.14 (Q), U76.2 (D), U76.14 (Q), U77.2 (D), U77.14 (Q), U78.2 (D), U78.14 (Q), U79.2 (D), U79.14 (Q), U80.2 (D), U80.14 (Q), U81.2 (D), U81.14 (Q)
RDQ3: U36.3 (D4), U61.12 (E), U62.2 (D), U62.14 (Q), U63.2 (D), U63.14 (Q), U64.2 (D), U64.14 (Q), U65.2 (D), U65.14 (Q), U66.2 (D), U66.14 (Q), U67.2 (D), U67.14 (Q), U68.2 (D), U68.14 (Q), U69.2 (D), U69.14 (Q), U73.17 (B1)
RDQ4: U48.15 (D1), U49.2 (D), U49.14 (Q), U50.2 (D), U50.14 (Q), U51.2 (D), U51.14 (Q), U52.2 (D), U52.14 (Q), U53.2 (D), U53.14 (Q), U54.2 (D), U54.14 (Q), U55.2 (D), U55.14 (Q), U56.2 (D), U56.14 (Q), U61.11 (D), U73.11 (B7)
RDQ5: U37.2 (D), U37.14 (Q), U38.2 (D), U38.14 (Q), U39.2 (D), U39.14 (Q), U40.2 (D), U40.14 (Q), U41.2 (D), U41.14 (Q), U42.2 (D), U42.14 (Q), U43.2 (D), U43.14 (Q), U44.2 (D), U44.14 (Q), U48.1 (D2), U61.10 (C), U73.16 (B2)
RDQ6: U25.2 (D), U25.14 (Q), U26.2 (D), U26.14 (Q), U27.2 (D), U27.14 (Q), U28.2 (D), U28.14 (Q), U29.2 (D), U29.14 (Q), U30.2 (D), U30.14 (Q), U31.2 (D), U31.14 (Q), U32.2 (D), U32.14 (Q), U48.2 (D3), U61.9 (B), U73.12 (B6)
RDQ7: U13.2 (D), U13.14 (Q), U14.2 (D), U14.14 (Q), U15.2 (D), U15.14 (Q), U16.2 (D), U16.14 (Q), U17.2 (D), U17.14 (Q), U18.2 (D), U18.14 (Q), U19.2 (D), U19.14 (Q), U20.2 (D), U20.14 (Q), U45.13 (D), U48.3 (D4), U61.8 (A), U73.15 (B3)
REFRESH: U33.4 (E1), U96.2, U96.8
RESET: J1.B2 (RESET), U47.9
RQP: U1.14 (Q), U2.14 (Q), U3.14 (Q), U4.14 (Q), U5.14 (Q), U6.14 (Q), U7.14 (Q), U8.14 (Q), U23.5
RRA0: RN1.6 (R3.2), U94.7 (Za)
RRA1: RN1.2 (R1.2), U94.9 (Zb)
RRA2: RN4.8 (R4.2), U95.7 (Za)
RRA3: RN4.5 (R3.1), U95.9 (Zb)
RRA4: RN1.4 (R2.2), U82.7 (Za)
RRA5: RN3.5 (R3.1), U82.9 (Zb)
RRA6: RN3.8 (R4.2), U70.7 (Za)
RRA7: RN3.4 (R2.2), U70.9 (Zb)
RRA8: RN3.1 (R1.1), U34.7 (Za)
RRDP: RN1.7 (R4.1), U61.5 (Even)
SW1: RN2.6 (R5), U12.1, U47.13, U59.9, U97.3
SW2: RN2.9 (R8), U11.13 (A2), U12.2, U97.1
SW3: RN2.8 (R7), U11.12 (A1), U12.3
SW4: RN2.7 (R6), U11.10 (A0), U12.4
SW5: RN2.4 (R3), U12.5, U24.1 (B3)
SW6: RN2.5 (R4), U12.6, U24.14 (B2)
SW7: RN2.2 (R1), U12.7, U24.11 (B1)
SW8: RN2.3 (R2), U12.8, U24.9 (B0)
UNK0: U36.10 (Q1), U82.11 (I1b), U85.4 (I1a)
UNK1: U36.9 (Q2), U70.5 (I1a), U85.6 (I2a)
UNK2: U36.7 (Q3), U70.11 (I1b), U85.8 (I3a)
UNK3: U34.5 (I1a), U36.6 (Q4), U85.11 (I0b)
UNK4: U35.5 (I1a), U48.10 (Q1), U85.13 (I1b)
UNK5: U35.11 (I1b), U48.9 (Q2), U85.15 (I2b)
UNK6: U48.7 (Q3), U72.11 (I1b), U85.17 (I3b)
UNK7: U48.6 (Q4), U85.2 (I0a)
UNKQ0: U45.4 (Q0), U58.3 (F)
UNKQ1: U45.5 (Q1), U58.13 (D)
UNKQ2: U45.6 (Q2), U58.9 (J)
UNKQ3: U45.7 (Q3), U58.5 (H)
UNKQ4: U45.9 (Q4), U46.1 (A6)
UNKQ5: U45.10 (Q5), U46.15 (A7)
UNKQ6: U45.11 (Q6), U46.14 (A8)
~ALLRAS: U9.2, U9.5, U9.10, U9.13, U10.2, U10.5, U10.10, U10.13, U96.3
~BMEMR: U57.11 (C), U59.13, U71.11
~BMEMW: RN4.3 (R2.1), U23.4, U23.9, U57.10 (~S), U71.3
~CAS0: U7.15 (~CAS), U19.15 (~CAS), U31.15 (~CAS), U33.15 (O0), U43.15 (~CAS), U55.15 (~CAS), U68.15 (~CAS), U80.15 (~CAS), U92.15 (~CAS), U105.15 (~CAS)
~CAS1: U8.15 (~CAS), U20.15 (~CAS), U32.15 (~CAS), U33.14 (O1), U44.15 (~CAS), U56.15 (~CAS), U69.15 (~CAS), U81.15 (~CAS), U93.15 (~CAS), U106.15 (~CAS)
~CAS2: U1.15 (~CAS), U13.15 (~CAS), U25.15 (~CAS), U33.13 (O2), U37.15 (~CAS), U49.15 (~CAS), U62.15 (~CAS), U74.15 (~CAS), U86.15 (~CAS), U99.15 (~CAS)
~CAS3: U2.15 (~CAS), U14.15 (~CAS), U26.15 (~CAS), U33.12 (O3), U38.15 (~CAS), U50.15 (~CAS), U63.15 (~CAS), U75.15 (~CAS), U87.15 (~CAS), U100.15 (~CAS)
~CAS4: U3.15 (~CAS), U15.15 (~CAS), U27.15 (~CAS), U33.11 (O4), U39.15 (~CAS), U51.15 (~CAS), U64.15 (~CAS), U76.15 (~CAS), U88.15 (~CAS), U101.15 (~CAS)
~CAS5: U4.15 (~CAS), U16.15 (~CAS), U28.15 (~CAS), U33.10 (O5), U40.15 (~CAS), U52.15 (~CAS), U65.15 (~CAS), U77.15 (~CAS), U89.15 (~CAS), U102.15 (~CAS)
~CAS6: U5.15 (~CAS), U17.15 (~CAS), U29.15 (~CAS), U33.9 (O6), U41.15 (~CAS), U53.15 (~CAS), U66.15 (~CAS), U78.15 (~CAS), U90.15 (~CAS), U103.15 (~CAS)
~CAS7: U6.15 (~CAS), U18.15 (~CAS), U30.15 (~CAS), U33.7 (O7), U42.15 (~CAS), U54.15 (~CAS), U67.15 (~CAS), U79.15 (~CAS), U91.15 (~CAS), U104.15 (~CAS)
~EMS_WINDOW: U35.2 (S1), U47.12, U58.8 (Y), U60.13, U71.5, U72.2 (S1)
~IOR: J1.B14 (~IOR), U83.13
~IOW: J1.B13 (~IOW), U83.1
~IO_CHCK: J1.A1 (~IO_CHCK), U97.12
~MEMR: J1.B12 (~SMEMR), U71.12, U96.12
~MEMSEL: U23.13, U33.5 (E2), U59.4, U59.12, U71.6
~MEMW: J1.B11 (~SMEMW), U71.1, U96.13
~PORT_RD: U83.11, U85.1 (OEa), U85.19 (OEb)
~PORT_WR: U23.12, U36.12 (~Ew), U45.14 (E), U48.12 (~Ew), U83.3
~RAMW: RN4.4 (R2.2), U1.3 (~W), U2.3 (~W), U3.3 (~W), U4.3 (~W), U5.3 (~W), U6.3 (~W), U7.3 (~W), U8.3 (~W), U13.3 (~W), U14.3 (~W), U15.3 (~W), U16.3 (~W), U17.3 (~W), U18.3 (~W), U19.3 (~W), U20.3 (~W), U25.3 (~W), U26.3 (~W), U27.3 (~W), U28.3 (~W), U29.3 (~W), U30.3 (~W), U31.3 (~W), U32.3 (~W), U37.3 (~W), U38.3 (~W), U39.3 (~W), U40.3 (~W), U41.3 (~W), U42.3 (~W), U43.3 (~W), U44.3 (~W), U49.3 (~W), U50.3 (~W), U51.3 (~W), U52.3 (~W), U53.3 (~W), U54.3 (~W), U55.3 (~W), U56.3 (~W), U62.3 (~W), U63.3 (~W), U64.3 (~W), U65.3 (~W), U66.3 (~W), U67.3 (~W), U68.3 (~W), U69.3 (~W), U74.3 (~W), U75.3 (~W), U76.3 (~W), U77.3 (~W), U78.3 (~W), U79.3 (~W), U80.3 (~W), U81.3 (~W), U86.3 (~W), U87.3 (~W), U88.3 (~W), U89.3 (~W), U90.3 (~W), U91.3 (~W), U92.3 (~W), U93.3 (~W), U99.3 (~W), U100.3 (~W), U101.3 (~W), U102.3 (~W), U103.3 (~W), U104.3 (~W), U105.3 (~W), U106.3 (~W)
~RAS0: U7.4 (~RAS), U9.3, U19.4 (~RAS), U31.4 (~RAS), U43.4 (~RAS), U55.4 (~RAS), U68.4 (~RAS), U80.4 (~RAS), U92.4 (~RAS), U105.4 (~RAS)
~RAS1: U8.4 (~RAS), U10.11, U20.4 (~RAS), U32.4 (~RAS), U44.4 (~RAS), U56.4 (~RAS), U69.4 (~RAS), U81.4 (~RAS), U93.4 (~RAS), U106.4 (~RAS)
~RAS2: U1.4 (~RAS), U10.8, U13.4 (~RAS), U25.4 (~RAS), U37.4 (~RAS), U49.4 (~RAS), U62.4 (~RAS), U74.4 (~RAS), U86.4 (~RAS), U99.4 (~RAS)
~RAS3: U2.4 (~RAS), U10.6, U14.4 (~RAS), U26.4 (~RAS), U38.4 (~RAS), U50.4 (~RAS), U63.4 (~RAS), U75.4 (~RAS), U87.4 (~RAS), U100.4 (~RAS)
~RAS4: U3.4 (~RAS), U9.6, U15.4 (~RAS), U27.4 (~RAS), U39.4 (~RAS), U51.4 (~RAS), U64.4 (~RAS), U76.4 (~RAS), U88.4 (~RAS), U101.4 (~RAS)
~RAS5: U4.4 (~RAS), U9.8, U16.4 (~RAS), U28.4 (~RAS), U40.4 (~RAS), U52.4 (~RAS), U65.4 (~RAS), U77.4 (~RAS), U89.4 (~RAS), U102.4 (~RAS)
~RAS6: U5.4 (~RAS), U9.11, U17.4 (~RAS), U29.4 (~RAS), U41.4 (~RAS), U53.4 (~RAS), U66.4 (~RAS), U78.4 (~RAS), U90.4 (~RAS), U103.4 (~RAS)
~RAS7: U6.4 (~RAS), U10.3, U18.4 (~RAS), U30.4 (~RAS), U42.4 (~RAS), U54.4 (~RAS), U67.4 (~RAS), U79.4 (~RAS), U91.4 (~RAS), U104.4 (~RAS)
~REFRESH: J1.B19 (~REFRESH), U96.10
~RESET: U45.15 (Clr), U47.8, U57.1 (~R)
~SW1: RN5.2 (R1.2), U60.1, U97.4
~SW2: RN2.10 (R9), U11.15 (A3), U97.2
~XMS_SEL: U47.6, U71.4

Notes on the sheet:
SWITCH POSITIONS (UP=0, DN=1) SW2 = 0: A19=1, A18=0 *** SW2 = 1: A19=0, A18=1 SW3 = 0: A17 = 0 *** SW3 = 1: A17 = 1 SW4 = 0: A16 = 0 *** SW4 = 1: A16 = 1 Lower memory address limit for extended memory: (Upper limit is fixed to 9FFFF) SW2,3,4 000: A19=1, A18=0, A17=0, A16=0. 0x80000 001: A19=1, A18=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
SWITCH POSITIONS (UP=0, DN=1) SW5,6,7,8: A7,A6,A5,A4 (A9=1, A8=0, A3=1, A2=0, A1=0) where A14,A15 select the page in the 4x4 register files. PPxx xx10 abcd 1000 = 0208, 0x0218, 0x0228, 0x0238, etc. A good default seems to be 0x0260 (?) This would be SW5=0, SW6=1, SW7=1, SW8=0.
UNKQ0-UNKQ3: Selects PROM outs 1-4. UNKQ4-UNKQ6: Selects PROM regions.
UNKQ4, UNKQ5, UNKQ6 through PROM (page starting address) 000 = O1=1 only at D000, O2=1 only at C400, O3=1 only at C800, O4=1 only at CC00 001 = O1=1 only at D000, O2=1 only at D400, O3=1 only at C800, O4=1 only at CC00 010 = O1=1 only at D000, O2=1 only at D400, O3=1 only at D800, O4=1 only at CC00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
ISA BUS BUFFERS
High for 00000 to 9FFFF.
Xebec Above Board Clone
PAGE REGISTERS
Low for A0000 to FFFFF.
DATA BUFFER PARITY HANDLER
EMS WINDOW MAPPER
This work is licensed under the Creative Commons Attribute-ShareAlike 4.0 International License. To view a copy of this license, visit http://creativecommons.org/license/by-sa/4.0/ or send a letter to Creative Commons, PO Box 1866, Mountain View, CA 94042, USA.
IO ADDRESS DECODER
CONFIG SWITCHES
RAS/CAS ADDRESS MUXES
RAS/CAS TIMING GEN
RAM CHIPS
RAS/CAS DECODER
Reversed by Tube Time
MEMORY ADDRESS DECODER
PARITY
